acdyer2025/ECE-2263-Final-Project/Design Report/Diagrams/connectionDiagram.png

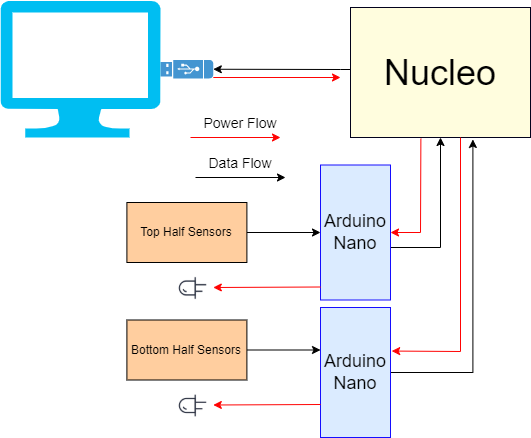
Design Report/Diagrams/connectionDiagram.png
