acdyer2025/ECE-2263-Final-Project/Design Report/Diagrams/iocFile.PNG

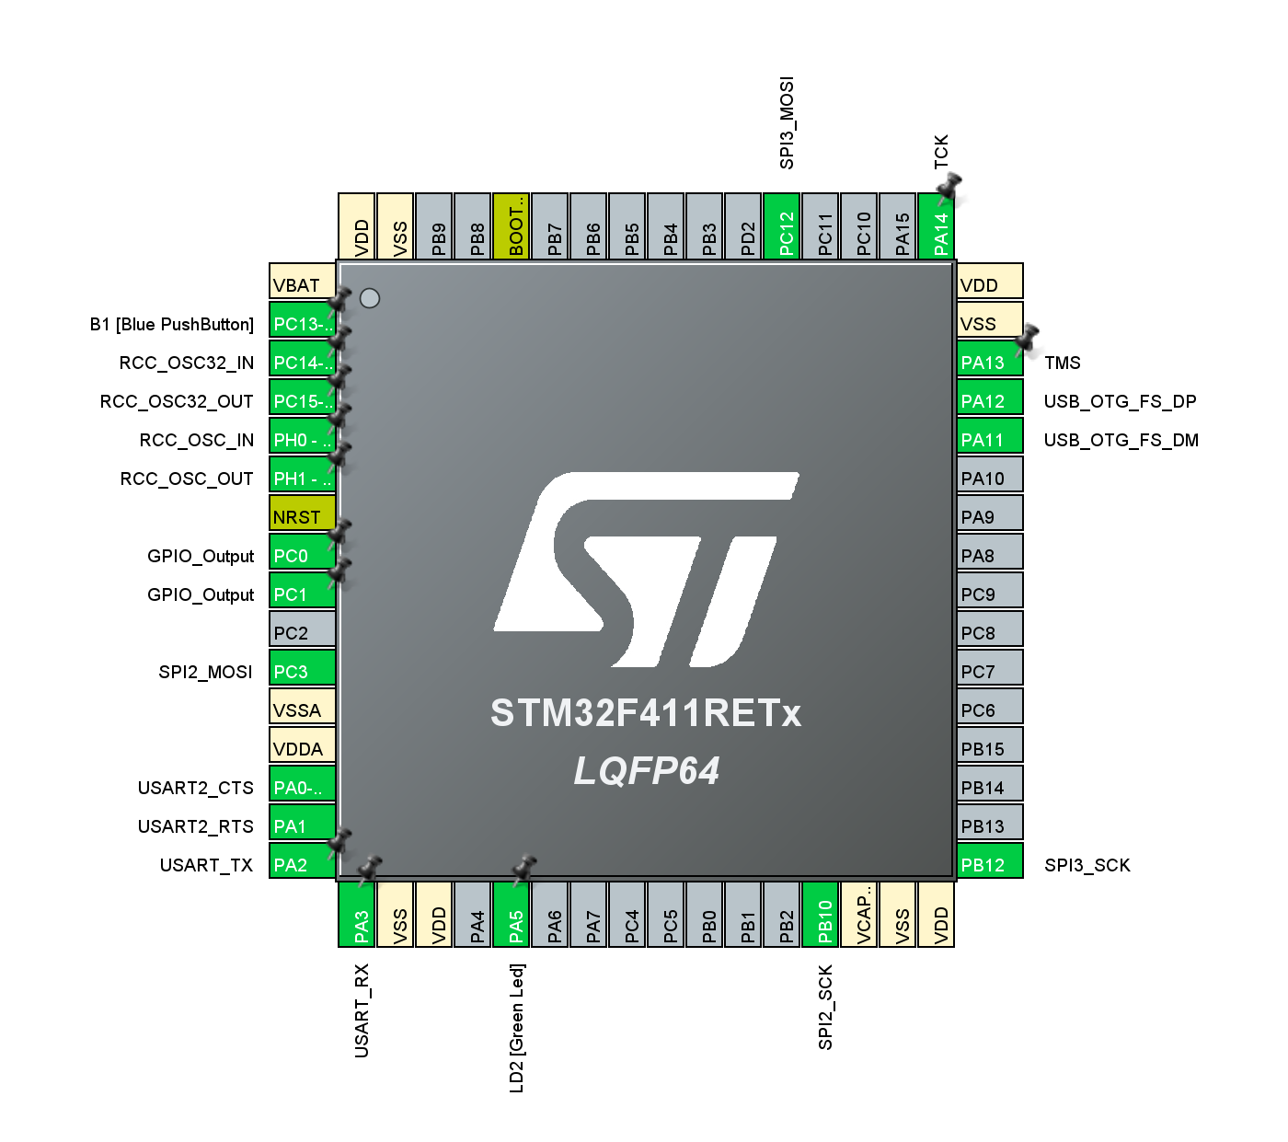
Design Report/Diagrams/iocFile.PNG
