acdyer2025/ECE-2263-Final-Project/Design Report/Diagrams/schematicDiagram.png

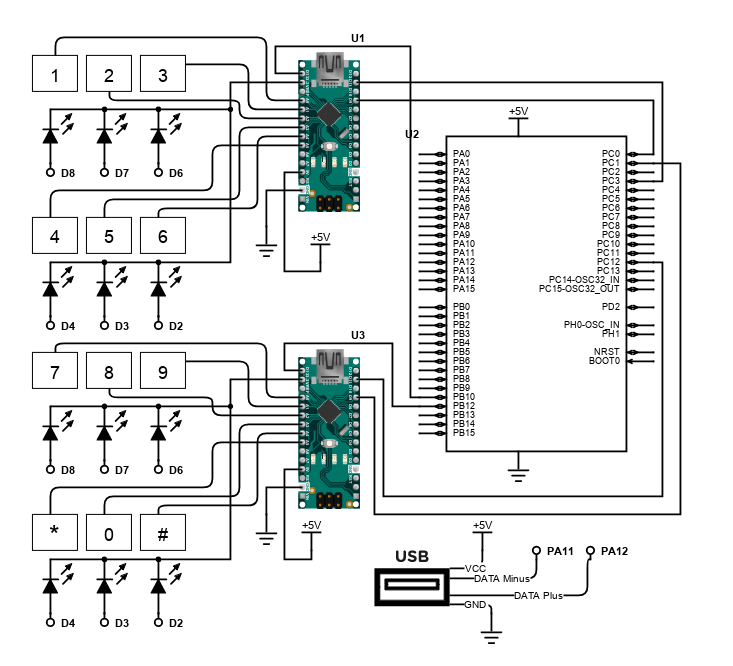
Design Report/Diagrams/schematicDiagram.png
