acdyer2025/ECE-2263-Final-Project/Design Report/Photos of Device/PXL_20211210_202542869.jpg

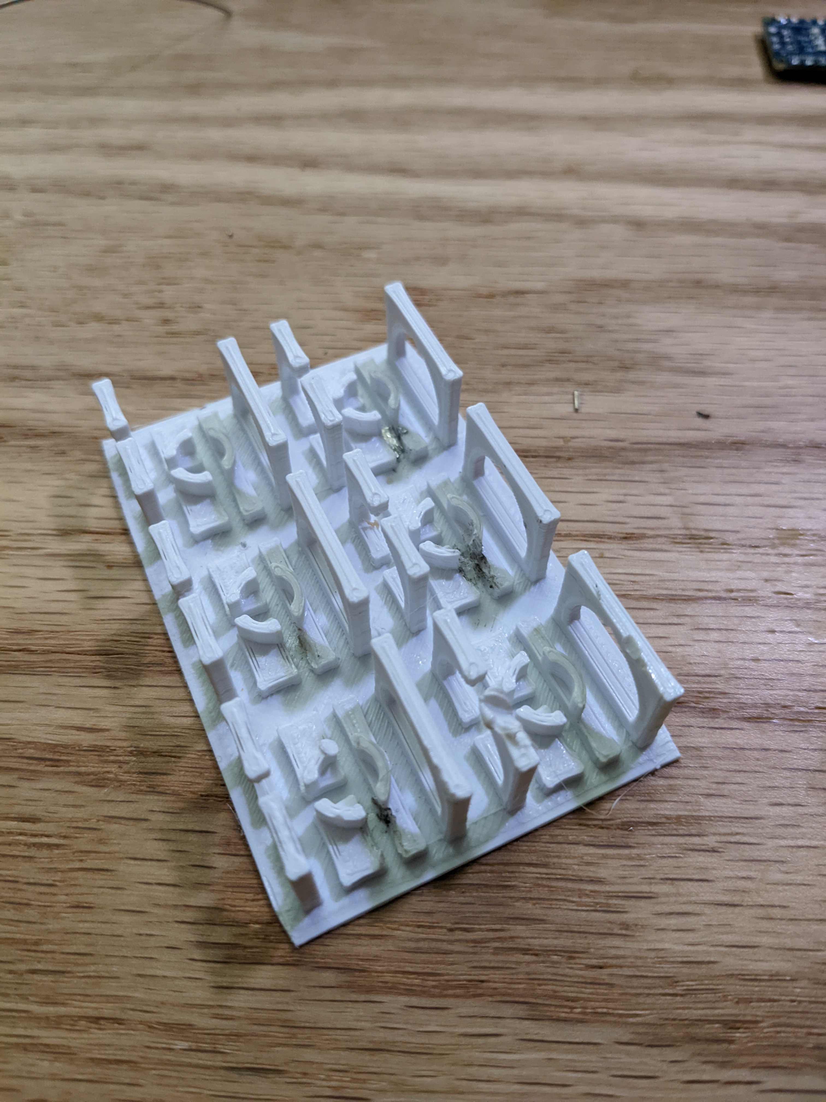
Design Report/Photos of Device/PXL_20211210_202542869.jpg
