acdyer2025/ECE-2263-Final-Project/Design Report/Photos of Device/PXL_20211210_233451572.jpg

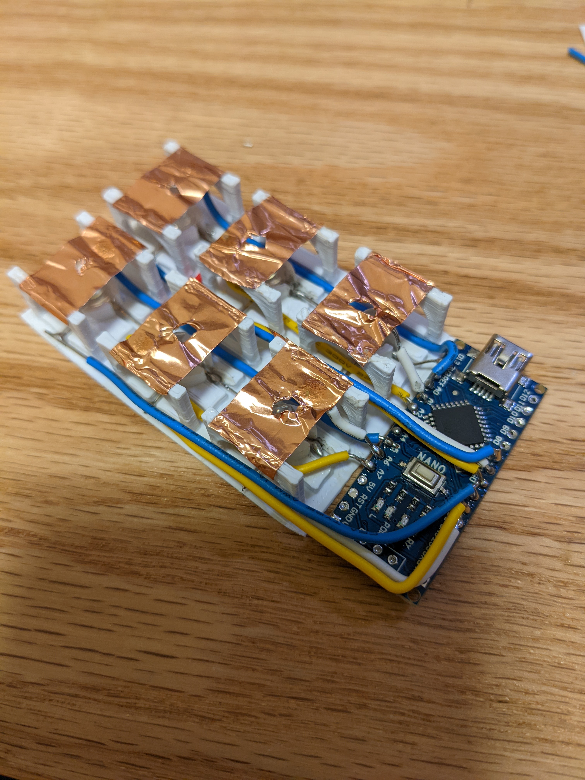
Design Report/Photos of Device/PXL_20211210_233451572.jpg
