acdyer2025/ECE-2263-Final-Project/Design Report/Photos of Device/PXL_20211210_233524437.jpg

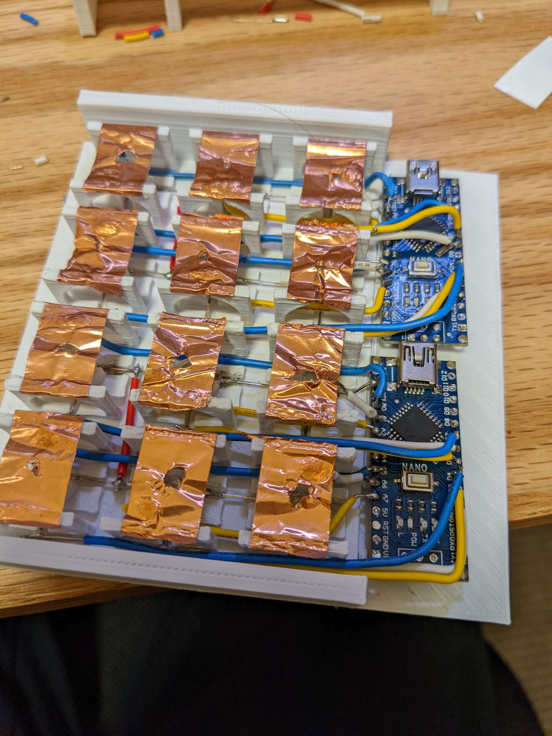
Design Report/Photos of Device/PXL_20211210_233524437.jpg
