acdyer2025/ECE-2263-Final-Project/Design Report/Photos of Device/PXL_20211211_000627328.jpg

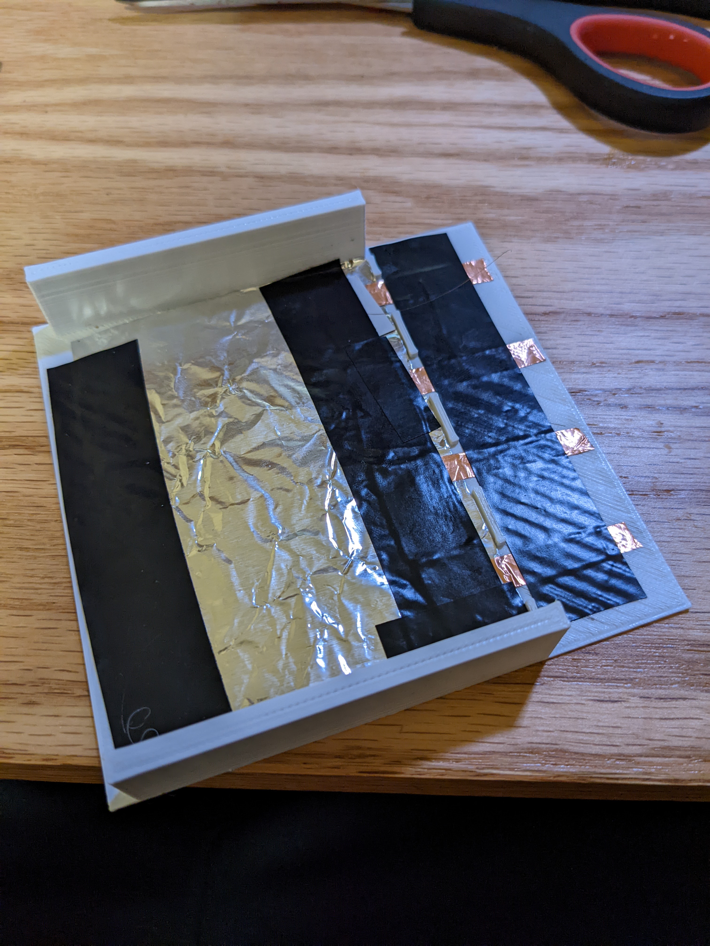
Design Report/Photos of Device/PXL_20211211_000627328.jpg
