acdyer2025/ECE-2263-Final-Project/Design Report/Photos of Device/PXL_20211211_012919116.jpg

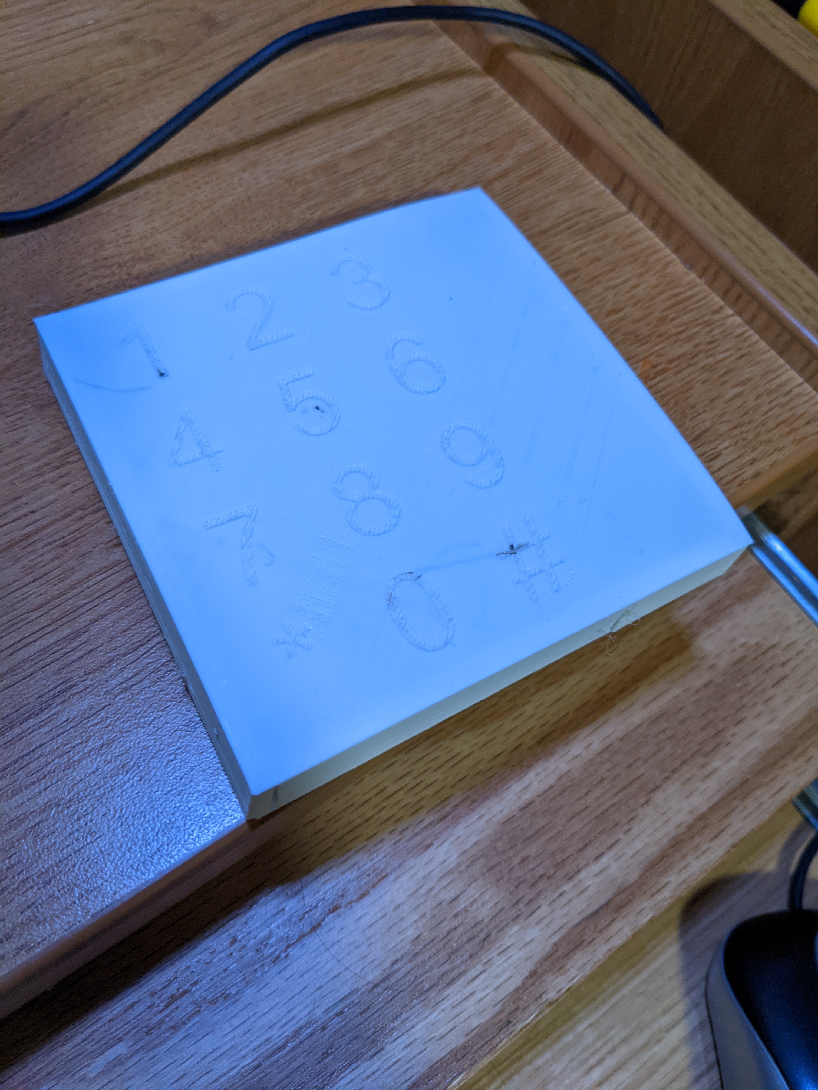
Design Report/Photos of Device/PXL_20211211_012919116.jpg
